yonatanStiebel/Splayer1/case/Splayer1 Case v3.stl

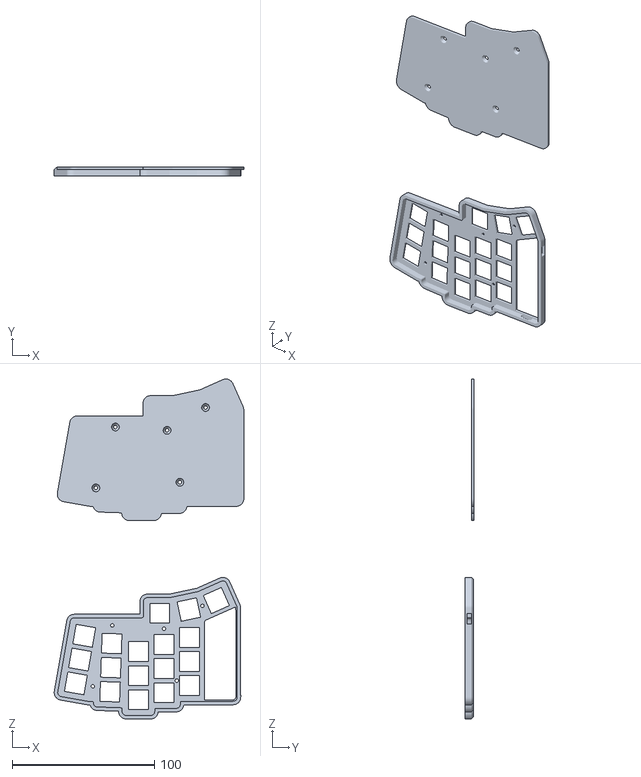
[picture p17: CAD file, 2024-04-24]
case/Splayer1 Case v3.stl
133.6 x 6.50 x 239.4
